RogerHao/cosmo-pager-radio-demo/pcb/cosmoradio-v4-carrier/output/renders/bottom.png

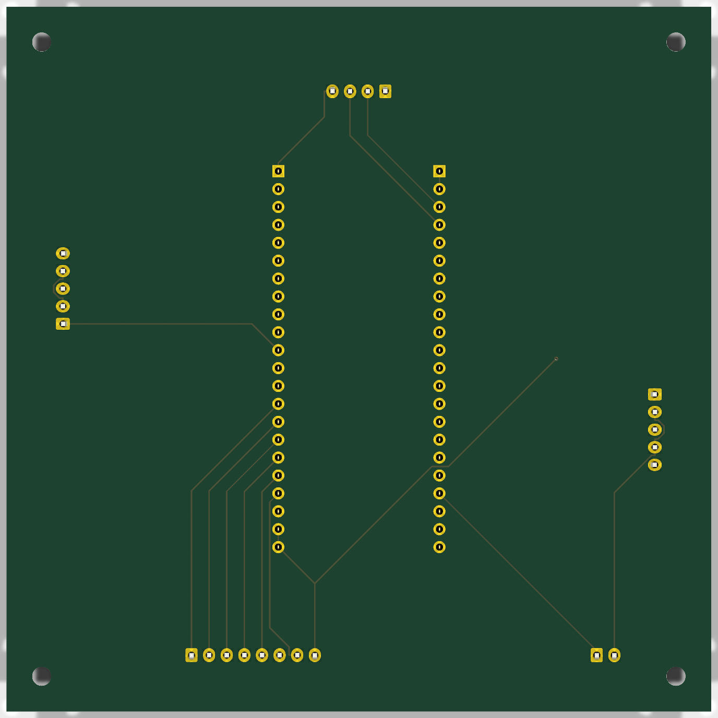
pcb/cosmoradio-v4-carrier/output/renders/bottom.png
