RogerHao/cosmo-pager-radio-demo/pcb/cosmoradio-v4-carrier/output/renders/iso.png

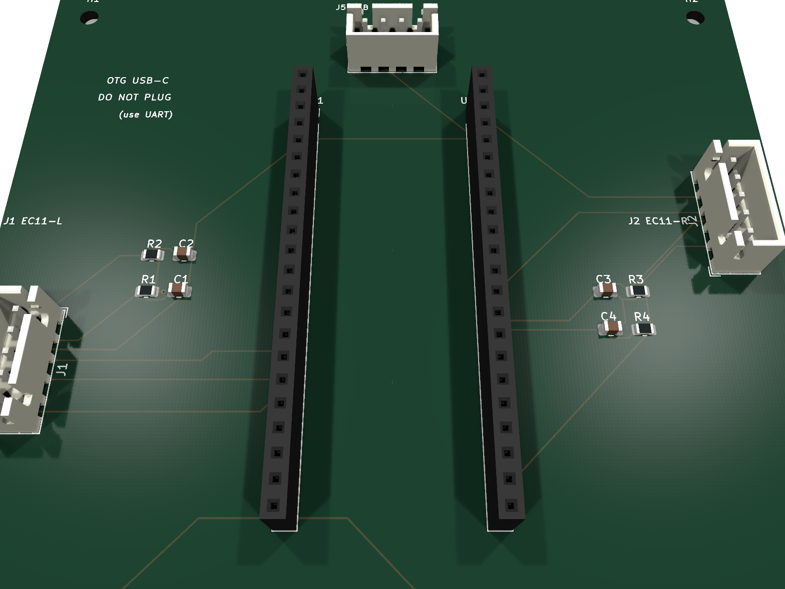
pcb/cosmoradio-v4-carrier/output/renders/iso.png
