RogerHao/cosmo-pager-radio-demo/pcb/cosmoradio-v4-carrier/output/renders/top.png

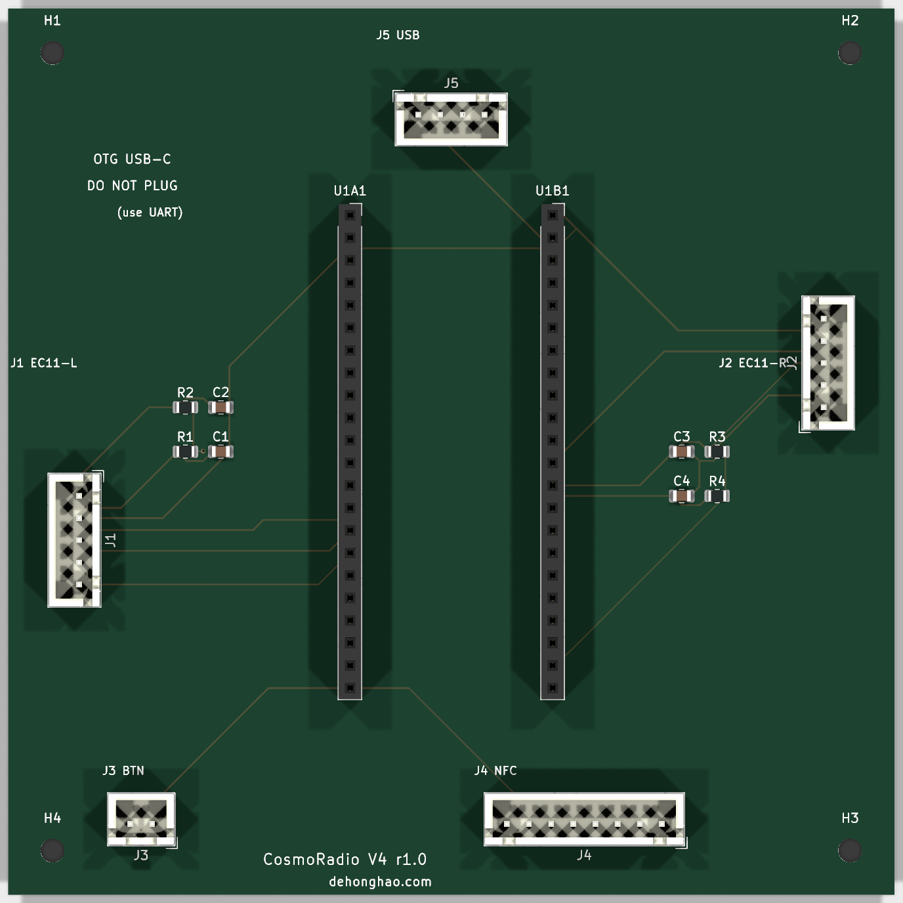
pcb/cosmoradio-v4-carrier/output/renders/top.png
