RogerHao/cosmo-pager-radio-demo/firmware/main/esp_hid_gap.c

/*
 * SPDX-FileCopyrightText: 2021-2024 Espressif Systems (Shanghai) CO LTD
 *
 * SPDX-License-Identifier: Unlicense OR CC0-1.0
 */


#include <string.h>
#include <stdbool.h>
#include <inttypes.h>

#include "freertos/FreeRTOS.h"
#include "freertos/task.h"
#include "freertos/semphr.h"

#include "esp_hid_gap.h"

#if CONFIG_BT_NIMBLE_ENABLED
#include "host/ble_hs.h"
#include "nimble/nimble_port.h"
#include "host/ble_gap.h"
#include "host/ble_hs_adv.h"
#include "nimble/ble.h"
#include "host/ble_sm.h"
#include "store/config/ble_store_config.h"
#else
#include "esp_bt_device.h"
#endif

static const char *TAG = "ESP_HID_GAP";

// uncomment to print all devices that were seen during a scan
#define GAP_DBG_PRINTF(...) //printf(__VA_ARGS__)
//static const char * gap_bt_prop_type_names[5] = {"","BDNAME","COD","RSSI","EIR"};

#if !CONFIG_BT_NIMBLE_ENABLED
static esp_hid_scan_result_t *bt_scan_results = NULL;
static size_t num_bt_scan_results = 0;

static esp_hid_scan_result_t *ble_scan_results = NULL;
static size_t num_ble_scan_results = 0;
#endif

static SemaphoreHandle_t bt_hidh_cb_semaphore = NULL;
#define WAIT_BT_CB() xSemaphoreTake(bt_hidh_cb_semaphore, portMAX_DELAY)
#define SEND_BT_CB() xSemaphoreGive(bt_hidh_cb_semaphore)

static SemaphoreHandle_t ble_hidh_cb_semaphore = NULL;
#define WAIT_BLE_CB() xSemaphoreTake(ble_hidh_cb_semaphore, portMAX_DELAY)
#define SEND_BLE_CB() xSemaphoreGive(ble_hidh_cb_semaphore)

#define SIZEOF_ARRAY(a) (sizeof(a)/sizeof(*a))

#if !CONFIG_BT_NIMBLE_ENABLED
static const char *ble_gap_evt_names[] = { "ADV_DATA_SET_COMPLETE", "SCAN_RSP_DATA_SET_COMPLETE", "SCAN_PARAM_SET_COMPLETE", "SCAN_RESULT", "ADV_DATA_RAW_SET_COMPLETE", "SCAN_RSP_DATA_RAW_SET_COMPLETE", "ADV_START_COMPLETE", "SCAN_START_COMPLETE", "AUTH_CMPL", "KEY", "SEC_REQ", "PASSKEY_NOTIF", "PASSKEY_REQ", "OOB_REQ", "LOCAL_IR", "LOCAL_ER", "NC_REQ", "ADV_STOP_COMPLETE", "SCAN_STOP_COMPLETE", "SET_STATIC_RAND_ADDR", "UPDATE_CONN_PARAMS", "SET_PKT_LENGTH_COMPLETE", "SET_LOCAL_PRIVACY_COMPLETE", "REMOVE_BOND_DEV_COMPLETE", "CLEAR_BOND_DEV_COMPLETE", "GET_BOND_DEV_COMPLETE", "READ_RSSI_COMPLETE", "UPDATE_WHITELIST_COMPLETE"};
static const char *bt_gap_evt_names[] = { "DISC_RES", "DISC_STATE_CHANGED", "RMT_SRVCS", "RMT_SRVC_REC", "AUTH_CMPL", "PIN_REQ", "CFM_REQ", "KEY_NOTIF", "KEY_REQ", "READ_RSSI_DELTA"};
static const char *ble_addr_type_names[] = {"PUBLIC", "RANDOM", "RPA_PUBLIC", "RPA_RANDOM"};

const char *ble_addr_type_str(esp_ble_addr_type_t ble_addr_type)
{
    if (ble_addr_type > BLE_ADDR_TYPE_RPA_RANDOM) {
        return "UNKNOWN";
    }
    return ble_addr_type_names[ble_addr_type];
}

const char *ble_gap_evt_str(uint8_t event)
{
    if (event >= SIZEOF_ARRAY(ble_gap_evt_names)) {
        return "UNKNOWN";
    }
    return ble_gap_evt_names[event];
}

const char *bt_gap_evt_str(uint8_t event)
{
    if (event >= SIZEOF_ARRAY(bt_gap_evt_names)) {
        return "UNKNOWN";
    }
    return bt_gap_evt_names[event];
}
#endif

#if CONFIG_BT_BLE_ENABLED
const char *esp_ble_key_type_str(esp_ble_key_type_t key_type)
{
    const char *key_str = NULL;
    switch (key_type) {
    case ESP_LE_KEY_NONE:
        key_str = "ESP_LE_KEY_NONE";
        break;
    case ESP_LE_KEY_PENC:
        key_str = "ESP_LE_KEY_PENC";
        break;
    case ESP_LE_KEY_PID:
        key_str = "ESP_LE_KEY_PID";
        break;
    case ESP_LE_KEY_PCSRK:
        key_str = "ESP_LE_KEY_PCSRK";
        break;
    case ESP_LE_KEY_PLK:
        key_str = "ESP_LE_KEY_PLK";
        break;
    case ESP_LE_KEY_LLK:
        key_str = "ESP_LE_KEY_LLK";
        break;
    case ESP_LE_KEY_LENC:
        key_str = "ESP_LE_KEY_LENC";
        break;
    case ESP_LE_KEY_LID:
        key_str = "ESP_LE_KEY_LID";
        break;
    case ESP_LE_KEY_LCSRK:
        key_str = "ESP_LE_KEY_LCSRK";
        break;
    default:
        key_str = "INVALID BLE KEY TYPE";
        break;

    }
    return key_str;
}
#endif /* CONFIG_BT_BLE_ENABLED */

#if !CONFIG_BT_NIMBLE_ENABLED
void esp_hid_scan_results_free(esp_hid_scan_result_t *results)
{
    esp_hid_scan_result_t *r = NULL;
    while (results) {
        r = results;
        results = results->next;
        if (r->name != NULL) {
            free((char *)r->name);
        }
        free(r);
    }
}
#endif

#if (CONFIG_BT_HID_DEVICE_ENABLED || CONFIG_BT_BLE_ENABLED)
static esp_hid_scan_result_t *find_scan_result(esp_bd_addr_t bda, esp_hid_scan_result_t *results)
{
    esp_hid_scan_result_t *r = results;
    while (r) {
        if (memcmp(bda, r->bda, sizeof(esp_bd_addr_t)) == 0) {
            return r;
        }
        r = r->next;
    }
    return NULL;
}
#endif /* (CONFIG_BT_HID_DEVICE_ENABLED || CONFIG_BT_BLE_ENABLED) */

#if CONFIG_BT_HID_DEVICE_ENABLED
static void add_bt_scan_result(esp_bd_addr_t bda, esp_bt_cod_t *cod, esp_bt_uuid_t *uuid, uint8_t *name, uint8_t name_len, int rssi)
{
    esp_hid_scan_result_t *r = find_scan_result(bda, bt_scan_results);
    if (r) {
        //Some info may come later
        if (r->name == NULL && name && name_len) {
            char *name_s = (char *)malloc(name_len + 1);
            if (name_s == NULL) {
                ESP_LOGE(TAG, "Malloc result name failed!");
                return;
            }
            memcpy(name_s, name, name_len);
            name_s[name_len] = 0;
            r->name = (const char *)name_s;
        }
        if (r->bt.uuid.len == 0 && uuid->len) {
            memcpy(&r->bt.uuid, uuid, sizeof(esp_bt_uuid_t));
        }
        if (rssi != 0) {
            r->rssi = rssi;
        }
        return;
    }

    r = (esp_hid_scan_result_t *)malloc(sizeof(esp_hid_scan_result_t));
    if (r == NULL) {
        ESP_LOGE(TAG, "Malloc bt_hidh_scan_result_t failed!");
        return;
    }
    r->transport = ESP_HID_TRANSPORT_BT;
    memcpy(r->bda, bda, sizeof(esp_bd_addr_t));
    memcpy(&r->bt.cod, cod, sizeof(esp_bt_cod_t));
    memcpy(&r->bt.uuid, uuid, sizeof(esp_bt_uuid_t));
    r->usage = esp_hid_usage_from_cod((uint32_t)cod);
    r->rssi = rssi;
    r->name = NULL;
    if (name_len && name) {
        char *name_s = (char *)malloc(name_len + 1);
        if (name_s == NULL) {
            free(r);
            ESP_LOGE(TAG, "Malloc result name failed!");
            return;
        }
        memcpy(name_s, name, name_len);
        name_s[name_len] = 0;
        r->name = (const char *)name_s;
    }
    r->next = bt_scan_results;
    bt_scan_results = r;
    num_bt_scan_results++;
}
#endif

#if CONFIG_BT_BLE_ENABLED
static void add_ble_scan_result(esp_bd_addr_t bda, esp_ble_addr_type_t addr_type, uint16_t appearance, uint8_t *name, uint8_t name_len, int rssi)
{
    if (find_scan_result(bda, ble_scan_results)) {
        ESP_LOGW(TAG, "Result already exists!");
        return;
    }
    esp_hid_scan_result_t *r = (esp_hid_scan_result_t *)malloc(sizeof(esp_hid_scan_result_t));
    if (r == NULL) {
        ESP_LOGE(TAG, "Malloc ble_hidh_scan_result_t failed!");
        return;
    }
    r->transport = ESP_HID_TRANSPORT_BLE;
    memcpy(r->bda, bda, sizeof(esp_bd_addr_t));
    r->ble.appearance = appearance;
    r->ble.addr_type = addr_type;
    r->usage = esp_hid_usage_from_appearance(appearance);
    r->rssi = rssi;
    r->name = NULL;
    if (name_len && name) {
        char *name_s = (char *)malloc(name_len + 1);
        if (name_s == NULL) {
            free(r);
            ESP_LOGE(TAG, "Malloc result name failed!");
            return;
        }
        memcpy(name_s, name, name_len);
        name_s[name_len] = 0;
        r->name = (const char *)name_s;
    }
    r->next = ble_scan_results;
    ble_scan_results = r;
    num_ble_scan_results++;
}
#endif /* CONFIG_BT_BLE_ENABLED */

#if !CONFIG_BT_NIMBLE_ENABLED
void print_uuid(esp_bt_uuid_t *uuid)
{
    if (uuid->len == ESP_UUID_LEN_16) {
        GAP_DBG_PRINTF("UUID16: 0x%04x", uuid->uuid.uuid16);
    } else if (uuid->len == ESP_UUID_LEN_32) {
        GAP_DBG_PRINTF("UUID32: 0x%08x", uuid->uuid.uuid32);
    } else if (uuid->len == ESP_UUID_LEN_128) {
        GAP_DBG_PRINTF("UUID128: %02x,%02x,%02x,%02x,%02x,%02x,%02x,%02x,%02x,%02x,%02x,%02x,%02x,%02x,%02x,%02x", uuid->uuid.uuid128[0],
                       uuid->uuid.uuid128[1], uuid->uuid.uuid128[2], uuid->uuid.uuid128[3],
                       uuid->uuid.uuid128[4], uuid->uuid.uuid128[5], uuid->uuid.uuid128[6],
                       uuid->uuid.uuid128[7], uuid->uuid.uuid128[8], uuid->uuid.uuid128[9],
                       uuid->uuid.uuid128[10], uuid->uuid.uuid128[11], uuid->uuid.uuid128[12],
                       uuid->uuid.uuid128[13], uuid->uuid.uuid128[14], uuid->uuid.uuid128[15]);
    }
}
#endif

#if CONFIG_BT_HID_DEVICE_ENABLED
static void handle_bt_device_result(struct disc_res_param *disc_res)
{
    GAP_DBG_PRINTF("BT : " ESP_BD_ADDR_STR, ESP_BD_ADDR_HEX(disc_res->bda));
    uint32_t codv = 0;
    esp_bt_cod_t *cod = (esp_bt_cod_t *)&codv;
    int8_t rssi = 0;
    uint8_t *name = NULL;
    uint8_t name_len = 0;
    esp_bt_uuid_t uuid;

    uuid.len = ESP_UUID_LEN_16;
    uuid.uuid.uuid16 = 0;

    for (int i = 0; i < disc_res->num_prop; i++) {
        esp_bt_gap_dev_prop_t *prop = &disc_res->prop[i];
        if (prop->type != ESP_BT_GAP_DEV_PROP_EIR) {
            GAP_DBG_PRINTF(", %s: ", gap_bt_prop_type_names[prop->type]);
        }
        if (prop->type == ESP_BT_GAP_DEV_PROP_BDNAME) {
            name = (uint8_t *)prop->val;
            name_len = strlen((const char *)name);
            GAP_DBG_PRINTF("%s", (const char *)name);
        } else if (prop->type == ESP_BT_GAP_DEV_PROP_RSSI) {
            rssi = *((int8_t *)prop->val);
            GAP_DBG_PRINTF("%d", rssi);
        } else if (prop->type == ESP_BT_GAP_DEV_PROP_COD) {
            memcpy(&codv, prop->val, sizeof(uint32_t));
            GAP_DBG_PRINTF("major: %s, minor: %d, service: 0x%03x", esp_hid_cod_major_str(cod->major), cod->minor, cod->service);
        } else if (prop->type == ESP_BT_GAP_DEV_PROP_EIR) {
            uint8_t len = 0;
            uint8_t *data = 0;

            data = esp_bt_gap_resolve_eir_data((uint8_t *)prop->val, ESP_BT_EIR_TYPE_CMPL_16BITS_UUID, &len);
            if (data == NULL) {
                data = esp_bt_gap_resolve_eir_data((uint8_t *)prop->val, ESP_BT_EIR_TYPE_INCMPL_16BITS_UUID, &len);
            }
            if (data && len == ESP_UUID_LEN_16) {
                uuid.len = ESP_UUID_LEN_16;
                uuid.uuid.uuid16 = data[0] + (data[1] << 8);
                GAP_DBG_PRINTF(", "); print_uuid(&uuid);
                continue;
            }

            data = esp_bt_gap_resolve_eir_data((uint8_t *)prop->val, ESP_BT_EIR_TYPE_CMPL_32BITS_UUID, &len);
            if (data == NULL) {
                data = esp_bt_gap_resolve_eir_data((uint8_t *)prop->val, ESP_BT_EIR_TYPE_INCMPL_32BITS_UUID, &len);
            }
            if (data && len == ESP_UUID_LEN_32) {
                uuid.len = len;
                memcpy(&uuid.uuid.uuid32, data, sizeof(uint32_t));
                GAP_DBG_PRINTF(", "); print_uuid(&uuid);
                continue;
            }

            data = esp_bt_gap_resolve_eir_data((uint8_t *)prop->val, ESP_BT_EIR_TYPE_CMPL_128BITS_UUID, &len);
            if (data == NULL) {
                data = esp_bt_gap_resolve_eir_data((uint8_t *)prop->val, ESP_BT_EIR_TYPE_INCMPL_128BITS_UUID, &len);
            }
            if (data && len == ESP_UUID_LEN_128) {
                uuid.len = len;
                memcpy(uuid.uuid.uuid128, (uint8_t *)data, len);
                GAP_DBG_PRINTF(", "); print_uuid(&uuid);
                continue;
            }

            //try to find a name
            if (name == NULL) {
                data = esp_bt_gap_resolve_eir_data((uint8_t *)prop->val, ESP_BT_EIR_TYPE_CMPL_LOCAL_NAME, &len);
                if (data == NULL) {
                    data = esp_bt_gap_resolve_eir_data((uint8_t *)prop->val, ESP_BT_EIR_TYPE_SHORT_LOCAL_NAME, &len);
                }
                if (data && len) {
                    name = data;
                    name_len = len;
                    GAP_DBG_PRINTF(", NAME: ");
                    for (int x = 0; x < len; x++) {
                        GAP_DBG_PRINTF("%c", (char)data[x]);
                    }
                }
            }
        }
    }
    GAP_DBG_PRINTF("\n");

    if (cod->major == ESP_BT_COD_MAJOR_DEV_PERIPHERAL || (find_scan_result(disc_res->bda, bt_scan_results) != NULL)) {
        add_bt_scan_result(disc_res->bda, cod, &uuid, name, name_len, rssi);
    }
}
#endif

#if CONFIG_BT_BLE_ENABLED
static void handle_ble_device_result(struct ble_scan_result_evt_param *scan_rst)
{

    uint16_t uuid = 0;
    uint16_t appearance = 0;
    char name[64] = {0};

    uint8_t uuid_len = 0;
    uint8_t *uuid_d = esp_ble_resolve_adv_data_by_type(scan_rst->ble_adv,
                      scan_rst->adv_data_len + scan_rst->scan_rsp_len,
                      ESP_BLE_AD_TYPE_16SRV_CMPL,
                      &uuid_len);
    if (uuid_d != NULL && uuid_len) {
        uuid = uuid_d[0] + (uuid_d[1] << 8);
    }

    uint8_t appearance_len = 0;
    uint8_t *appearance_d = esp_ble_resolve_adv_data_by_type(scan_rst->ble_adv,
                                                    scan_rst->adv_data_len + scan_rst->scan_rsp_len,
                                                    ESP_BLE_AD_TYPE_APPEARANCE,
                                                    &appearance_len);
    if (appearance_d != NULL && appearance_len) {
        appearance = appearance_d[0] + (appearance_d[1] << 8);
    }

    uint8_t adv_name_len = 0;
    uint8_t *adv_name = esp_ble_resolve_adv_data_by_type(scan_rst->ble_adv,
                                                 scan_rst->adv_data_len + scan_rst->scan_rsp_len,
                                                 ESP_BLE_AD_TYPE_NAME_CMPL,
                                                 &adv_name_len);

    if (adv_name == NULL) {
        adv_name = esp_ble_resolve_adv_data_by_type(scan_rst->ble_adv,
                                            scan_rst->adv_data_len + scan_rst->scan_rsp_len,
                                            ESP_BLE_AD_TYPE_NAME_SHORT,
                                            &adv_name_len);
    }

    if (adv_name != NULL && adv_name_len) {
        memcpy(name, adv_name, adv_name_len);
        name[adv_name_len] = 0;
    }

    GAP_DBG_PRINTF("BLE: " ESP_BD_ADDR_STR ", ", ESP_BD_ADDR_HEX(scan_rst->bda));
    GAP_DBG_PRINTF("RSSI: %d, ", scan_rst->rssi);
    GAP_DBG_PRINTF("UUID: 0x%04x, ", uuid);
    GAP_DBG_PRINTF("APPEARANCE: 0x%04x, ", appearance);
    GAP_DBG_PRINTF("ADDR_TYPE: '%s'", ble_addr_type_str(scan_rst->ble_addr_type));
    if (adv_name_len) {
        GAP_DBG_PRINTF(", NAME: '%s'", name);
    }
    GAP_DBG_PRINTF("\n");

    if (uuid == ESP_GATT_UUID_HID_SVC) {
        add_ble_scan_result(scan_rst->bda, scan_rst->ble_addr_type, appearance, adv_name, adv_name_len, scan_rst->rssi);
    }
}
#endif /* CONFIG_BT_BLE_ENABLED */

#if CONFIG_BT_HID_DEVICE_ENABLED
/*
 * BT GAP
 * */

static void bt_gap_event_handler(esp_bt_gap_cb_event_t event, esp_bt_gap_cb_param_t *param)
{
    switch (event) {
    case ESP_BT_GAP_DISC_STATE_CHANGED_EVT: {
        ESP_LOGV(TAG, "BT GAP DISC_STATE %s", (param->disc_st_chg.state == ESP_BT_GAP_DISCOVERY_STARTED) ? "START" : "STOP");
        if (param->disc_st_chg.state == ESP_BT_GAP_DISCOVERY_STOPPED) {
            SEND_BT_CB();
        }
        break;
    }
    case ESP_BT_GAP_DISC_RES_EVT: {
        handle_bt_device_result(&param->disc_res);
        break;
    }
    case ESP_BT_GAP_PIN_REQ_EVT: {
        ESP_LOGI(TAG, "BT GAP PIN_REQ_EVT min_16_digit:%d", param->pin_req.min_16_digit);
        if (param->pin_req.min_16_digit) {
            ESP_LOGI(TAG, "Input pin code: 0000 0000 0000 0000");
            esp_bt_pin_code_t pin_code = {0};
            esp_bt_gap_pin_reply(param->pin_req.bda, true, 16, pin_code);
        } else {
            ESP_LOGI(TAG, "Input pin code: 1234");
            esp_bt_pin_code_t pin_code;
            pin_code[0] = '1';
            pin_code[1] = '2';
            pin_code[2] = '3';
            pin_code[3] = '4';
            esp_bt_gap_pin_reply(param->pin_req.bda, true, 4, pin_code);
        }
        break;
    }

#if (CONFIG_EXAMPLE_SSP_ENABLED == true)
    case ESP_BT_GAP_CFM_REQ_EVT:
        ESP_LOGI(TAG, "BT GAP CFM_REQ_EVT Please compare the numeric value: %06" PRIu32,
                 param->cfm_req.num_val);
        esp_bt_gap_ssp_confirm_reply(param->cfm_req.bda, true);
        break;
    case ESP_BT_GAP_KEY_NOTIF_EVT:
        ESP_LOGI(TAG, "BT GAP KEY_NOTIF_EVT passkey:%06" PRIu32, param->key_notif.passkey);
        break;
    case ESP_BT_GAP_KEY_REQ_EVT:
        ESP_LOGI(TAG, "BT GAP KEY_REQ_EVT Please enter passkey!");
        break;
#endif
    case ESP_BT_GAP_MODE_CHG_EVT:
        ESP_LOGI(TAG, "BT GAP MODE_CHG_EVT mode:%d", param->mode_chg.mode);
        break;
    default:
        ESP_LOGV(TAG, "BT GAP EVENT %s", bt_gap_evt_str(event));
        break;
    }
}

static esp_err_t init_bt_gap(void)
{
    esp_err_t ret;
#if (CONFIG_EXAMPLE_SSP_ENABLED)
    /* Set default parameters for Secure Simple Pairing */
    esp_bt_sp_param_t param_type = ESP_BT_SP_IOCAP_MODE;
    esp_bt_io_cap_t iocap = ESP_BT_IO_CAP_NONE;
    esp_bt_gap_set_security_param(param_type, &iocap, sizeof(uint8_t));
#endif
    /*
     * Set default parameters for Legacy Pairing
     * Use fixed pin code
     */
    esp_bt_pin_type_t pin_type = ESP_BT_PIN_TYPE_FIXED;
    esp_bt_pin_code_t pin_code;
    pin_code[0] = '1';
    pin_code[1] = '2';
    pin_code[2] = '3';
    pin_code[3] = '4';
    esp_bt_gap_set_pin(pin_type, 4, pin_code);

    if ((ret = esp_bt_gap_register_callback(bt_gap_event_handler)) != ESP_OK) {
        ESP_LOGE(TAG, "esp_bt_gap_register_callback failed: %d", ret);
        return ret;
    }

    // Allow BT devices to connect back to us
    if ((ret = esp_bt_gap_set_scan_mode(ESP_BT_CONNECTABLE, ESP_BT_NON_DISCOVERABLE)) != ESP_OK) {
        ESP_LOGE(TAG, "esp_bt_gap_set_scan_mode failed: %d", ret);
        return ret;
    }
    return ret;
}

static esp_err_t start_bt_scan(uint32_t seconds)
{
    esp_err_t ret = ESP_OK;
    if ((ret = esp_bt_gap_start_discovery(ESP_BT_INQ_MODE_GENERAL_INQUIRY, (int)(seconds / 1.28), 0)) != ESP_OK) {
        ESP_LOGE(TAG, "esp_bt_gap_start_discovery failed: %d", ret);
        return ret;
    }
    return ret;
}
#endif

#if CONFIG_BT_BLE_ENABLED
/*
 * BLE GAP
 * */
extern void ble_hid_task_start_up(void);
static void ble_gap_event_handler(esp_gap_ble_cb_event_t event, esp_ble_gap_cb_param_t *param)
{
    switch (event) {
    /*
     * SCAN
     * */
    case ESP_GAP_BLE_SCAN_PARAM_SET_COMPLETE_EVT: {
        ESP_LOGV(TAG, "BLE GAP EVENT SCAN_PARAM_SET_COMPLETE");
        SEND_BLE_CB();
        break;
    }
    case ESP_GAP_BLE_SCAN_RESULT_EVT: {
        esp_ble_gap_cb_param_t *scan_result = (esp_ble_gap_cb_param_t *)param;
        switch (scan_result->scan_rst.search_evt) {
        case ESP_GAP_SEARCH_INQ_RES_EVT: {
            handle_ble_device_result(&scan_result->scan_rst);
            break;
        }
        case ESP_GAP_SEARCH_INQ_CMPL_EVT:
            ESP_LOGV(TAG, "BLE GAP EVENT SCAN DONE: %d", scan_result->scan_rst.num_resps);
            SEND_BLE_CB();
            break;
        default:
            break;
        }
        break;
    }
    case ESP_GAP_BLE_SCAN_STOP_COMPLETE_EVT: {
        ESP_LOGV(TAG, "BLE GAP EVENT SCAN CANCELED");
        break;
    }

    /*
     * ADVERTISEMENT
     * */
    case ESP_GAP_BLE_ADV_DATA_SET_COMPLETE_EVT:
        ESP_LOGV(TAG, "BLE GAP ADV_DATA_SET_COMPLETE");
        break;

    case ESP_GAP_BLE_ADV_START_COMPLETE_EVT:
        ESP_LOGV(TAG, "BLE GAP ADV_START_COMPLETE");
        break;

    /*
     * AUTHENTICATION
     * */
    case ESP_GAP_BLE_AUTH_CMPL_EVT:
        if (!param->ble_security.auth_cmpl.success) {
            // if AUTH ERROR,hid maybe don't work.
            ESP_LOGE(TAG, "BLE GAP AUTH ERROR: 0x%x", param->ble_security.auth_cmpl.fail_reason);
        } else {
            ESP_LOGI(TAG, "BLE GAP AUTH SUCCESS");
        }
        ble_hid_task_start_up();
        break;

    case ESP_GAP_BLE_KEY_EVT: //shows the ble key info share with peer device to the user.
        ESP_LOGI(TAG, "BLE GAP KEY type = %s", esp_ble_key_type_str(param->ble_security.ble_key.key_type));
        break;

    case ESP_GAP_BLE_PASSKEY_NOTIF_EVT: // ESP_IO_CAP_OUT
        // The app will receive this evt when the IO has Output capability and the peer device IO has Input capability.
        // Show the passkey number to the user to input it in the peer device.
        ESP_LOGI(TAG, "BLE GAP PASSKEY_NOTIF passkey:%"PRIu32, param->ble_security.key_notif.passkey);
        break;

    case ESP_GAP_BLE_NC_REQ_EVT: // ESP_IO_CAP_IO
        // The app will receive this event when the IO has DisplayYesNO capability and the peer device IO also has DisplayYesNo capability.
        // show the passkey number to the user to confirm it with the number displayed by peer device.
        ESP_LOGI(TAG, "BLE GAP NC_REQ passkey:%"PRIu32, param->ble_security.key_notif.passkey);
        esp_ble_confirm_reply(param->ble_security.key_notif.bd_addr, true);
        break;

    case ESP_GAP_BLE_PASSKEY_REQ_EVT: // ESP_IO_CAP_IN
        // The app will receive this evt when the IO has Input capability and the peer device IO has Output capability.
        // See the passkey number on the peer device and send it back.
        ESP_LOGI(TAG, "BLE GAP PASSKEY_REQ");
        //esp_ble_passkey_reply(param->ble_security.ble_req.bd_addr, true, 1234);
        break;

    case ESP_GAP_BLE_SEC_REQ_EVT:
        ESP_LOGI(TAG, "BLE GAP SEC_REQ");
        // Send the positive(true) security response to the peer device to accept the security request.
        // If not accept the security request, should send the security response with negative(false) accept value.
        esp_ble_gap_security_rsp(param->ble_security.ble_req.bd_addr, true);
        break;

    default:
        ESP_LOGV(TAG, "BLE GAP EVENT %s", ble_gap_evt_str(event));
        break;
    }
}

static esp_err_t init_ble_gap(void)
{
    esp_err_t ret;

    if ((ret = esp_ble_gap_register_callback(ble_gap_event_handler)) != ESP_OK) {
        ESP_LOGE(TAG, "esp_ble_gap_register_callback failed: %d", ret);
        return ret;
    }
    return ret;
}

static esp_ble_scan_params_t hid_scan_params = {
    .scan_type              = BLE_SCAN_TYPE_ACTIVE,
    .own_addr_type          = BLE_ADDR_TYPE_PUBLIC,
    .scan_filter_policy     = BLE_SCAN_FILTER_ALLOW_ALL,
    .scan_interval          = 0x50,
    .scan_window            = 0x30,
    .scan_duplicate         = BLE_SCAN_DUPLICATE_ENABLE,
};

static esp_err_t start_ble_scan(uint32_t seconds)
{
    esp_err_t ret = ESP_OK;
    if ((ret = esp_ble_gap_set_scan_params(&hid_scan_params)) != ESP_OK) {
        ESP_LOGE(TAG, "esp_ble_gap_set_scan_params failed: %d", ret);
        return ret;
    }
    WAIT_BLE_CB();

    if ((ret = esp_ble_gap_start_scanning(seconds)) != ESP_OK) {
        ESP_LOGE(TAG, "esp_ble_gap_start_scanning failed: %d", ret);
        return ret;
    }
    return ret;
}

#if !CONFIG_BT_NIMBLE_ENABLED
esp_err_t esp_hid_ble_gap_adv_init(uint16_t appearance, const char *device_name)
{

    esp_err_t ret;

    const uint8_t hidd_service_uuid128[] = {
        0xfb, 0x34, 0x9b, 0x5f, 0x80, 0x00, 0x00, 0x80, 0x00, 0x10, 0x00, 0x00, 0x12, 0x18, 0x00, 0x00,
    };

    esp_ble_adv_data_t ble_adv_data = {
        .set_scan_rsp = false,
        .include_name = true,
        .include_txpower = true,
        .min_interval = 0x0006, //slave connection min interval, Time = min_interval * 1.25 msec
        .max_interval = 0x0010, //slave connection max interval, Time = max_interval * 1.25 msec
        .appearance = appearance,
        .manufacturer_len = 0,
        .p_manufacturer_data =  NULL,
        .service_data_len = 0,
        .p_service_data = NULL,
        .service_uuid_len = sizeof(hidd_service_uuid128),
        .p_service_uuid = (uint8_t *)hidd_service_uuid128,
        .flag = 0x6,
    };

    esp_ble_auth_req_t auth_req = ESP_LE_AUTH_REQ_SC_MITM_BOND;
    //esp_ble_io_cap_t iocap = ESP_IO_CAP_OUT;//you have to enter the key on the host
    //esp_ble_io_cap_t iocap = ESP_IO_CAP_IN;//you have to enter the key on the device
    esp_ble_io_cap_t iocap = ESP_IO_CAP_IO;//you have to agree that key matches on both
    //esp_ble_io_cap_t iocap = ESP_IO_CAP_NONE;//device is not capable of input or output, insecure
    uint8_t init_key = ESP_BLE_ENC_KEY_MASK | ESP_BLE_ID_KEY_MASK;
    uint8_t rsp_key = ESP_BLE_ENC_KEY_MASK | ESP_BLE_ID_KEY_MASK;
    uint8_t key_size = 16; //the key size should be 7~16 bytes
    uint32_t passkey = 1234;//ESP_IO_CAP_OUT

    if ((ret = esp_ble_gap_set_security_param(ESP_BLE_SM_AUTHEN_REQ_MODE, &auth_req, 1)) != ESP_OK) {
        ESP_LOGE(TAG, "GAP set_security_param AUTHEN_REQ_MODE failed: %d", ret);
        return ret;
    }

    if ((ret = esp_ble_gap_set_security_param(ESP_BLE_SM_IOCAP_MODE, &iocap, 1)) != ESP_OK) {
        ESP_LOGE(TAG, "GAP set_security_param IOCAP_MODE failed: %d", ret);
        return ret;
    }

    if ((ret = esp_ble_gap_set_security_param(ESP_BLE_SM_SET_INIT_KEY, &init_key, 1)) != ESP_OK) {
        ESP_LOGE(TAG, "GAP set_security_param SET_INIT_KEY failed: %d", ret);
        return ret;
    }

    if ((ret = esp_ble_gap_set_security_param(ESP_BLE_SM_SET_RSP_KEY, &rsp_key, 1)) != ESP_OK) {
        ESP_LOGE(TAG, "GAP set_security_param SET_RSP_KEY failed: %d", ret);
        return ret;
    }

    if ((ret = esp_ble_gap_set_security_param(ESP_BLE_SM_MAX_KEY_SIZE, &key_size, 1)) != ESP_OK) {
        ESP_LOGE(TAG, "GAP set_security_param MAX_KEY_SIZE failed: %d", ret);
        return ret;
    }

    if ((ret = esp_ble_gap_set_security_param(ESP_BLE_SM_SET_STATIC_PASSKEY, &passkey, sizeof(uint32_t))) != ESP_OK) {
        ESP_LOGE(TAG, "GAP set_security_param SET_STATIC_PASSKEY failed: %d", ret);
        return ret;
    }

    if ((ret = esp_ble_gap_set_device_name(device_name)) != ESP_OK) {
        ESP_LOGE(TAG, "GAP set_device_name failed: %d", ret);
        return ret;
    }

    if ((ret = esp_ble_gap_config_adv_data(&ble_adv_data)) != ESP_OK) {
        ESP_LOGE(TAG, "GAP config_adv_data failed: %d", ret);
        return ret;
    }

    return ret;
}
#endif
esp_err_t esp_hid_ble_gap_adv_start(void)
{
    static esp_ble_adv_params_t hidd_adv_params = {
        .adv_int_min        = 0x20,
        .adv_int_max        = 0x30,
        .adv_type           = ADV_TYPE_IND,
        .own_addr_type      = BLE_ADDR_TYPE_PUBLIC,
        .channel_map        = ADV_CHNL_ALL,
        .adv_filter_policy  = ADV_FILTER_ALLOW_SCAN_ANY_CON_ANY,
    };
    return esp_ble_gap_start_advertising(&hidd_adv_params);
}
#endif /* CONFIG_BT_BLE_ENABLED */

#if CONFIG_BT_NIMBLE_ENABLED
#define GATT_SVR_SVC_HID_UUID 0x1812

extern void ble_hid_task_start_up(void);
static struct ble_hs_adv_fields fields;

esp_err_t esp_hid_ble_gap_adv_init(uint16_t appearance, const char *device_name)
{
    ble_uuid16_t *uuid16, *uuid16_1;
    /**
     *  Set the advertisement data included in our advertisements:
     *     o Flags (indicates advertisement type and other general info).
     *     o Advertising tx power.
     *     o Device name.
     *     o 16-bit service UUIDs (HID).
     */

    memset(&fields, 0, sizeof fields);

    /* Advertise two flags:
     *     o Discoverability in forthcoming advertisement (general)
     *     o BLE-only (BR/EDR unsupported).
     */
    fields.flags = BLE_HS_ADV_F_DISC_GEN |
                   BLE_HS_ADV_F_BREDR_UNSUP;

    fields.appearance = ESP_HID_APPEARANCE_GENERIC;
    fields.appearance_is_present = 1;

    /* Indicate that the TX power level field should be included; have the
     * stack fill this value automatically.  This is done by assigning the
     * special value BLE_HS_ADV_TX_PWR_LVL_AUTO.
     */
    fields.tx_pwr_lvl_is_present = 1;
    fields.tx_pwr_lvl = BLE_HS_ADV_TX_PWR_LVL_AUTO;

    fields.name = (uint8_t *)device_name;
    fields.name_len = strlen(device_name);
    fields.name_is_complete = 1;

    uuid16 = (ble_uuid16_t *)malloc(sizeof(ble_uuid16_t));
    uuid16_1 = (ble_uuid16_t[]) {
        BLE_UUID16_INIT(GATT_SVR_SVC_HID_UUID)
    };
    memcpy(uuid16, uuid16_1, sizeof(ble_uuid16_t));
    fields.uuids16 = uuid16;
    fields.num_uuids16 = 1;
    fields.uuids16_is_complete = 1;

    /* Initialize the security configuration */
    /* Use "Just Works" pairing - no PIN required */
    ble_hs_cfg.sm_io_cap = BLE_SM_IO_CAP_NO_IO;
    ble_hs_cfg.sm_bonding = 1;
    ble_hs_cfg.sm_mitm = 0;  // Disable MITM for Just Works
    ble_hs_cfg.sm_sc = 1;
    ble_hs_cfg.sm_our_key_dist = BLE_SM_PAIR_KEY_DIST_ID | BLE_SM_PAIR_KEY_DIST_ENC;
    ble_hs_cfg.sm_their_key_dist |= BLE_SM_PAIR_KEY_DIST_ID | BLE_SM_PAIR_KEY_DIST_ENC;

    return ESP_OK;

}

// Connection state for reconnection logic
typedef enum {
    CONN_STATE_IDLE = 0,
    CONN_STATE_ADVERTISING,
    CONN_STATE_CONNECTED,
    CONN_STATE_DISCONNECTED,
} conn_state_t;

static conn_state_t s_conn_state = CONN_STATE_IDLE;
static uint16_t s_conn_handle = 0;

// Bonded peer address for directed advertising
static ble_addr_t s_last_bonded_peer = {0};
static bool s_has_bonded_peer = false;

// Keepalive task handle
static TaskHandle_t s_keepalive_task = NULL;
#define KEEPALIVE_INTERVAL_MS 30000
#define RSSI_WARNING_THRESHOLD  -70
#define RSSI_CRITICAL_THRESHOLD -85

// Forward declarations
static void start_advertising_with_retry(void);
static esp_err_t start_directed_advertising(const ble_addr_t *peer_addr);
static void keepalive_task(void *pvParameters);

// Get disconnect reason string for debugging
static const char* get_disconnect_reason_str(uint8_t reason)
{
    switch (reason) {
    case 0x08: return "CONNECTION_TIMEOUT";
    case 0x13: return "REMOTE_USER_TERMINATED";
    case 0x16: return "LOCAL_HOST_TERMINATED";
    case 0x05: return "AUTHENTICATION_FAILURE";
    case 0x06: return "PIN_OR_KEY_MISSING";
    case 0x3B: return "UNACCEPTABLE_CONN_PARAMS";
    case 0x3D: return "CONN_FAILED_ESTABLISHMENT";
    default:   return "UNKNOWN";
    }
}

// Check if peer is bonded (has stored keys)
static bool is_peer_bonded(const ble_addr_t *peer_addr)
{
    int rc;
    struct ble_store_value_sec value_sec;
    struct ble_store_key_sec key_sec;

    memset(&key_sec, 0, sizeof(key_sec));
    key_sec.peer_addr = *peer_addr;

    rc = ble_store_read_peer_sec(&key_sec, &value_sec);
    return (rc == 0);
}

static int
nimble_hid_gap_event(struct ble_gap_event *event, void *arg)
{
    struct ble_gap_conn_desc desc;
    int rc;

    switch (event->type) {
    case BLE_GAP_EVENT_CONNECT:
        /* A new connection was established or a connection attempt failed. */
        ESP_LOGI(TAG, "connection %s; status=%d",
                event->connect.status == 0 ? "established" : "failed",
                event->connect.status);
        if (event->connect.status == 0) {
            s_conn_state = CONN_STATE_CONNECTED;
            s_conn_handle = event->connect.conn_handle;

            // Get connection details and save peer address for directed advertising
            rc = ble_gap_conn_find(event->connect.conn_handle, &desc);
            if (rc == 0) {
                memcpy(&s_last_bonded_peer, &desc.peer_id_addr, sizeof(ble_addr_t));
                s_has_bonded_peer = true;
                ESP_LOGI(TAG, "Connected to %02X:%02X:%02X:%02X:%02X:%02X, handle=%d",
                         desc.peer_id_addr.val[5], desc.peer_id_addr.val[4],
                         desc.peer_id_addr.val[3], desc.peer_id_addr.val[2],
                         desc.peer_id_addr.val[1], desc.peer_id_addr.val[0],
                         s_conn_handle);
            } else {
                ESP_LOGI(TAG, "Connected, handle=%d", s_conn_handle);
            }

            // Optimize connection parameters for HID responsiveness
            // Priority: stability over power consumption
            struct ble_gap_upd_params conn_params = {
                .itvl_min = 8,              // 10ms (8 * 1.25ms) - fast response
                .itvl_max = 16,             // 20ms (16 * 1.25ms) - max latency 20ms
                .latency = 0,               // No skipping - always respond immediately
                .supervision_timeout = 400, // 4 seconds (400 * 10ms)
            };
            rc = ble_gap_update_params(s_conn_handle, &conn_params);
            if (rc != 0) {
                ESP_LOGW(TAG, "Failed to update connection params: %d", rc);
            } else {
                ESP_LOGI(TAG, "Connection params update requested: itvl=8-16, latency=0, timeout=400");
            }

            // Start keepalive task
            if (s_keepalive_task == NULL) {
                xTaskCreate(keepalive_task, "keepalive", 2048, NULL, 5, &s_keepalive_task);
                ESP_LOGI(TAG, "Keepalive task started");
            }
        } else {
            // Connection failed, restart advertising
            s_conn_state = CONN_STATE_DISCONNECTED;
            ESP_LOGW(TAG, "Connection failed, restarting advertising");
            start_advertising_with_retry();
        }
        return 0;
        break;
    case BLE_GAP_EVENT_DISCONNECT:
        ESP_LOGI(TAG, "Disconnected: reason=0x%02x (%s)",
                 event->disconnect.reason,
                 get_disconnect_reason_str(event->disconnect.reason));
        s_conn_state = CONN_STATE_DISCONNECTED;
        s_conn_handle = 0;

        // Stop keepalive task
        if (s_keepalive_task != NULL) {
            vTaskDelete(s_keepalive_task);
            s_keepalive_task = NULL;
            ESP_LOGI(TAG, "Keepalive task stopped");
        }

        // Handle based on disconnect reason
        switch (event->disconnect.reason) {
        case 0x08:  // CONNECTION_TIMEOUT - try fast reconnect
            ESP_LOGI(TAG, "Connection timeout, attempting directed advertising");
            if (s_has_bonded_peer && is_peer_bonded(&s_last_bonded_peer)) {
                start_directed_advertising(&s_last_bonded_peer);
            } else {
                start_advertising_with_retry();
            }
            break;

        case 0x13:  // REMOTE_USER_TERMINATED - delay before reconnect
            ESP_LOGI(TAG, "Remote user disconnected, waiting before reconnect");
            vTaskDelay(pdMS_TO_TICKS(1000));
            start_advertising_with_retry();
            break;

        case 0x05:  // AUTHENTICATION_FAILURE
        case 0x06:  // PIN_OR_KEY_MISSING
            ESP_LOGW(TAG, "Authentication failed, clearing bond and restarting");
            if (s_has_bonded_peer) {
                ble_store_util_delete_peer(&s_last_bonded_peer);
                s_has_bonded_peer = false;
            }
            start_advertising_with_retry();
            break;

        default:
            ESP_LOGI(TAG, "Auto-restarting advertising after disconnect");
            start_advertising_with_retry();
            break;
        }

        return 0;
    case BLE_GAP_EVENT_CONN_UPDATE:
        /* The central has updated the connection parameters. */
        ESP_LOGI(TAG, "connection updated; status=%d",
                event->conn_update.status);
        return 0;

    case BLE_GAP_EVENT_ADV_COMPLETE:
        ESP_LOGI(TAG, "advertise complete; reason=%d", event->adv_complete.reason);
        // If not connected, restart advertising
        if (s_conn_state != CONN_STATE_CONNECTED) {
            ESP_LOGI(TAG, "Advertising timeout, restarting...");
            start_advertising_with_retry();
        }
        return 0;

    case BLE_GAP_EVENT_SUBSCRIBE:
        ESP_LOGI(TAG, "subscribe event; conn_handle=%d attr_handle=%d "
                "reason=%d prevn=%d curn=%d previ=%d curi=%d\n",
                event->subscribe.conn_handle,
                event->subscribe.attr_handle,
                event->subscribe.reason,
                event->subscribe.prev_notify,
                event->subscribe.cur_notify,
                event->subscribe.prev_indicate,
                event->subscribe.cur_indicate);
        return 0;

    case BLE_GAP_EVENT_MTU:
        ESP_LOGI(TAG, "mtu update event; conn_handle=%d cid=%d mtu=%d",
                event->mtu.conn_handle,
                event->mtu.channel_id,
                event->mtu.value);
        return 0;

    case BLE_GAP_EVENT_ENC_CHANGE:
        /* Encryption has been enabled or disabled for this connection. */
        MODLOG_DFLT(INFO, "encryption change event; status=%d ",
                event->enc_change.status);
        rc = ble_gap_conn_find(event->enc_change.conn_handle, &desc);
        assert(rc == 0);
        ble_hid_task_start_up();
        return 0;

    case BLE_GAP_EVENT_NOTIFY_TX:
        MODLOG_DFLT(INFO, "notify_tx event; conn_handle=%d attr_handle=%d "
                "status=%d is_indication=%d",
                event->notify_tx.conn_handle,
                event->notify_tx.attr_handle,
                event->notify_tx.status,
                event->notify_tx.indication);
        return 0;

    case BLE_GAP_EVENT_REPEAT_PAIRING:
        /* We already have a bond with the peer, but it is attempting to
         * establish a new secure link.  This app sacrifices security for
         * convenience: just throw away the old bond and accept the new link.
         */

        /* Delete the old bond. */
        rc = ble_gap_conn_find(event->repeat_pairing.conn_handle, &desc);
        assert(rc == 0);
        ble_store_util_delete_peer(&desc.peer_id_addr);

        /* Return BLE_GAP_REPEAT_PAIRING_RETRY to indicate that the host should
         * continue with the pairing operation.
         */
        return BLE_GAP_REPEAT_PAIRING_RETRY;

    case BLE_GAP_EVENT_PASSKEY_ACTION:
        ESP_LOGI(TAG, "PASSKEY_ACTION_EVENT started");
        struct ble_sm_io pkey = {0};
        int key = 0;

        if (event->passkey.params.action == BLE_SM_IOACT_DISP) {
            pkey.action = event->passkey.params.action;
            pkey.passkey = 123456; // This is the passkey to be entered on peer
            ESP_LOGI(TAG, "Enter passkey %" PRIu32 "on the peer side", pkey.passkey);
            rc = ble_sm_inject_io(event->passkey.conn_handle, &pkey);
            ESP_LOGI(TAG, "ble_sm_inject_io result: %d", rc);
        } else if (event->passkey.params.action == BLE_SM_IOACT_NUMCMP) {
            ESP_LOGI(TAG, "Accepting passkey..");
            pkey.action = event->passkey.params.action;
            pkey.numcmp_accept = key;
            rc = ble_sm_inject_io(event->passkey.conn_handle, &pkey);
            ESP_LOGI(TAG, "ble_sm_inject_io result: %d", rc);
        } else if (event->passkey.params.action == BLE_SM_IOACT_OOB) {
            static uint8_t tem_oob[16] = {0};
            pkey.action = event->passkey.params.action;
            for (int i = 0; i < 16; i++) {
                pkey.oob[i] = tem_oob[i];
            }
            rc = ble_sm_inject_io(event->passkey.conn_handle, &pkey);
            ESP_LOGI(TAG, "ble_sm_inject_io result: %d", rc);
        } else if (event->passkey.params.action == BLE_SM_IOACT_INPUT) {
            ESP_LOGI(TAG, "Input not supported passing -> 123456");
            pkey.action = event->passkey.params.action;
            pkey.passkey = 123456;
            rc = ble_sm_inject_io(event->passkey.conn_handle, &pkey);
            ESP_LOGI(TAG, "ble_sm_inject_io result: %d", rc);
        }
        return 0;
    }
    return 0;
}
// Start directed advertising to a specific peer for fast reconnection
static esp_err_t start_directed_advertising(const ble_addr_t *peer_addr)
{
    int rc;
    struct ble_gap_adv_params adv_params;

    // Stop any current advertising first
    ble_gap_adv_stop();

    memset(&adv_params, 0, sizeof(adv_params));
    adv_params.conn_mode = BLE_GAP_CONN_MODE_DIR;  // Directed advertising
    adv_params.disc_mode = BLE_GAP_DISC_MODE_NON;  // Not discoverable to others
    adv_params.high_duty_cycle = 1;                // High duty cycle for fast reconnect

    ESP_LOGI(TAG, "Starting directed advertising to %02X:%02X:%02X:%02X:%02X:%02X",
             peer_addr->val[5], peer_addr->val[4], peer_addr->val[3],
             peer_addr->val[2], peer_addr->val[1], peer_addr->val[0]);

    // Directed advertising with 1.28s timeout (BLE spec limit for high duty cycle)
    rc = ble_gap_adv_start(BLE_OWN_ADDR_PUBLIC, peer_addr, 1280,
                           &adv_params, nimble_hid_gap_event, NULL);
    if (rc != 0) {
        ESP_LOGW(TAG, "Directed advertising failed: %d, falling back to undirected", rc);
        // Fall back to normal advertising
        return esp_hid_ble_gap_adv_start();
    }

    s_conn_state = CONN_STATE_ADVERTISING;
    return ESP_OK;
}

// Keepalive task - sends empty HID reports to maintain connection
static void keepalive_task(void *pvParameters)
{
    ESP_LOGI(TAG, "Keepalive task running, interval=%dms", KEEPALIVE_INTERVAL_MS);

    while (1) {
        vTaskDelay(pdMS_TO_TICKS(KEEPALIVE_INTERVAL_MS));

        if (s_conn_state != CONN_STATE_CONNECTED || s_conn_handle == 0) {
            continue;
        }

        // Read RSSI for connection quality monitoring
        int8_t rssi = 0;
        int rc = ble_gap_conn_rssi(s_conn_handle, &rssi);
        if (rc == 0) {
            if (rssi < RSSI_CRITICAL_THRESHOLD) {
                ESP_LOGW(TAG, "Keepalive: RSSI=%d (CRITICAL - connection at risk)", rssi);
            } else if (rssi < RSSI_WARNING_THRESHOLD) {
                ESP_LOGI(TAG, "Keepalive: RSSI=%d (weak signal)", rssi);
            } else {
                ESP_LOGI(TAG, "Keepalive: RSSI=%d (good)", rssi);
            }
        }

        // Send empty HID report as keepalive
        // This is handled by the HID device layer - just log that we're alive
        ESP_LOGD(TAG, "Keepalive: connection active");
    }
}

// Helper to restart advertising with error handling
static void start_advertising_with_retry(void)
{
    // Small delay before restarting to avoid rapid cycling
    vTaskDelay(pdMS_TO_TICKS(100));

    int rc = esp_hid_ble_gap_adv_start();
    if (rc != 0) {
        ESP_LOGW(TAG, "Failed to restart advertising: %d, will retry", rc);
        // Schedule another retry after longer delay
        vTaskDelay(pdMS_TO_TICKS(1000));
        rc = esp_hid_ble_gap_adv_start();
        if (rc != 0) {
            ESP_LOGE(TAG, "Advertising restart failed again: %d", rc);
        }
    } else {
        s_conn_state = CONN_STATE_ADVERTISING;
        ESP_LOGI(TAG, "Advertising restarted successfully");
    }
}

esp_err_t esp_hid_ble_gap_adv_start(void)
{
    int rc;
    struct ble_gap_adv_params adv_params;
    /* Indefinite advertising for HID device (0 = no timeout) */
    int32_t adv_duration_ms = BLE_HS_FOREVER;

    rc = ble_gap_adv_set_fields(&fields);
    if (rc != 0) {
        MODLOG_DFLT(ERROR, "error setting advertisement data; rc=%d\n", rc);
        return rc;
    }
    /* Begin advertising. */
    memset(&adv_params, 0, sizeof adv_params);
    adv_params.conn_mode = BLE_GAP_CONN_MODE_UND;
    adv_params.disc_mode = BLE_GAP_DISC_MODE_GEN;
    adv_params.itvl_min = BLE_GAP_ADV_ITVL_MS(30);/* Recommended interval 30ms to 50ms */
    adv_params.itvl_max = BLE_GAP_ADV_ITVL_MS(50);
    rc = ble_gap_adv_start(BLE_OWN_ADDR_PUBLIC, NULL, adv_duration_ms,
                           &adv_params, nimble_hid_gap_event, NULL);
    if (rc != 0) {
        MODLOG_DFLT(ERROR, "error enabling advertisement; rc=%d\n", rc);
        return rc;
    }
    return rc;
}
#endif


/*
 * CONTROLLER INIT
 * */

#if !CONFIG_BT_NIMBLE_ENABLED
static esp_err_t init_low_level(uint8_t mode)
{
    esp_err_t ret;
    esp_bt_controller_config_t bt_cfg = BT_CONTROLLER_INIT_CONFIG_DEFAULT();
#if CONFIG_IDF_TARGET_ESP32
    bt_cfg.mode = mode;
#endif
#if CONFIG_BT_HID_DEVICE_ENABLED
    if (mode & ESP_BT_MODE_CLASSIC_BT) {
        bt_cfg.bt_max_acl_conn = 3;
        bt_cfg.bt_max_sync_conn = 3;
    } else
#endif
    {
        ret = esp_bt_controller_mem_release(ESP_BT_MODE_CLASSIC_BT);
        if (ret) {
            ESP_LOGE(TAG, "esp_bt_controller_mem_release failed: %d", ret);
            return ret;
        }
    }
    ret = esp_bt_controller_init(&bt_cfg);
    if (ret) {
        ESP_LOGE(TAG, "esp_bt_controller_init failed: %d", ret);
        return ret;
    }

    ret = esp_bt_controller_enable(mode);
    if (ret) {
        ESP_LOGE(TAG, "esp_bt_controller_enable failed: %d", ret);
        return ret;
    }

    esp_bluedroid_config_t bluedroid_cfg = BT_BLUEDROID_INIT_CONFIG_DEFAULT();
#if (CONFIG_EXAMPLE_SSP_ENABLED == false)
    bluedroid_cfg.ssp_en = false;
#endif
    ret = esp_bluedroid_init_with_cfg(&bluedroid_cfg);
    if (ret) {
        ESP_LOGE(TAG, "esp_bluedroid_init failed: %d", ret);
        return ret;
    }

    ret = esp_bluedroid_enable();
    if (ret) {
        ESP_LOGE(TAG, "esp_bluedroid_enable failed: %d", ret);
        return ret;
    }
#if CONFIG_BT_HID_DEVICE_ENABLED
    if (mode & ESP_BT_MODE_CLASSIC_BT) {
        ret = init_bt_gap();
        if (ret) {
            return ret;
        }
    }
#endif
#if CONFIG_BT_BLE_ENABLED
    if (mode & ESP_BT_MODE_BLE) {
        ret = init_ble_gap();
        if (ret) {
            return ret;
        }
    }
#endif /* CONFIG_BT_BLE_ENABLED */
    return ret;
}
#endif

#if CONFIG_BT_NIMBLE_ENABLED
static esp_err_t init_low_level(uint8_t mode)
{
    esp_err_t ret;
    esp_bt_controller_config_t bt_cfg = BT_CONTROLLER_INIT_CONFIG_DEFAULT();
#if CONFIG_IDF_TARGET_ESP32
    bt_cfg.mode = mode;
#endif
    ret = esp_bt_controller_mem_release(ESP_BT_MODE_CLASSIC_BT);
    if (ret) {
        ESP_LOGE(TAG, "esp_bt_controller_mem_release failed: %d", ret);
        return ret;
    }
    ret = esp_bt_controller_init(&bt_cfg);
    if (ret) {
        ESP_LOGE(TAG, "esp_bt_controller_init failed: %d", ret);
        return ret;
    }

    ret = esp_bt_controller_enable(mode);
    if (ret) {
        ESP_LOGE(TAG, "esp_bt_controller_enable failed: %d", ret);
        return ret;
    }

    ret = esp_nimble_init();
    if (ret) {
        ESP_LOGE(TAG, "esp_nimble_init failed: %d", ret);
        return ret;
    }


    return ret;
}
#endif

esp_err_t esp_hid_gap_init(uint8_t mode)
{
    esp_err_t ret;
    if (!mode || mode > ESP_BT_MODE_BTDM) {
        ESP_LOGE(TAG, "Invalid mode given!");
        return ESP_FAIL;
    }

    if (bt_hidh_cb_semaphore != NULL) {
        ESP_LOGE(TAG, "Already initialised");
        return ESP_FAIL;
    }

    bt_hidh_cb_semaphore = xSemaphoreCreateBinary();
    if (bt_hidh_cb_semaphore == NULL) {
        ESP_LOGE(TAG, "xSemaphoreCreateMutex failed!");
        return ESP_FAIL;
    }

    ble_hidh_cb_semaphore = xSemaphoreCreateBinary();
    if (ble_hidh_cb_semaphore == NULL) {
        ESP_LOGE(TAG, "xSemaphoreCreateMutex failed!");
        vSemaphoreDelete(bt_hidh_cb_semaphore);
        bt_hidh_cb_semaphore = NULL;
        return ESP_FAIL;
    }

    ret = init_low_level(mode);
    if (ret != ESP_OK) {
        vSemaphoreDelete(bt_hidh_cb_semaphore);
        bt_hidh_cb_semaphore = NULL;
        vSemaphoreDelete(ble_hidh_cb_semaphore);
        ble_hidh_cb_semaphore = NULL;
        return ret;
    }

    return ESP_OK;
}

#if CONFIG_BT_NIMBLE_ENABLED
// Public API implementations

void keepalive_start(void)
{
    if (s_keepalive_task == NULL && s_conn_state == CONN_STATE_CONNECTED) {
        xTaskCreate(keepalive_task, "keepalive", 2048, NULL, 5, &s_keepalive_task);
        ESP_LOGI(TAG, "Keepalive task started manually");
    }
}

void keepalive_stop(void)
{
    if (s_keepalive_task != NULL) {
        vTaskDelete(s_keepalive_task);
        s_keepalive_task = NULL;
        ESP_LOGI(TAG, "Keepalive task stopped manually");
    }
}

bool esp_hid_ble_is_connected(void)
{
    return (s_conn_state == CONN_STATE_CONNECTED);
}

uint16_t esp_hid_ble_get_conn_handle(void)
{
    return s_conn_handle;
}
#endif

#if !CONFIG_BT_NIMBLE_ENABLED
esp_err_t esp_hid_scan(uint32_t seconds, size_t *num_results, esp_hid_scan_result_t **results)
{
    if (num_bt_scan_results || bt_scan_results || num_ble_scan_results || ble_scan_results) {
        ESP_LOGE(TAG, "There are old scan results. Free them first!");
        return ESP_FAIL;
    }

#if CONFIG_BT_BLE_ENABLED
    if (start_ble_scan(seconds) == ESP_OK) {
        WAIT_BLE_CB();
    } else {
        return ESP_FAIL;
    }
#endif /* CONFIG_BT_BLE_ENABLED */

#if CONFIG_BT_HID_DEVICE_ENABLED
    if (start_bt_scan(seconds) == ESP_OK) {
        WAIT_BT_CB();
    } else {
        return ESP_FAIL;
    }
#endif

    *num_results = num_bt_scan_results + num_ble_scan_results;
    *results = bt_scan_results;
    if (num_bt_scan_results) {
        while (bt_scan_results->next != NULL) {
            bt_scan_results = bt_scan_results->next;
        }
        bt_scan_results->next = ble_scan_results;
    } else {
        *results = ble_scan_results;
    }

    num_bt_scan_results = 0;
    bt_scan_results = NULL;
    num_ble_scan_results = 0;
    ble_scan_results = NULL;
    return ESP_OK;
}
#endif
