RogerHao/cosmo-pager-radio-demo/firmware/main/esp_hid_gap.h

/*
 * SPDX-FileCopyrightText: 2021-2023 Espressif Systems (Shanghai) CO LTD
 *
 * SPDX-License-Identifier: Unlicense OR CC0-1.0
 */

#ifndef _ESP_HID_GAP_H_
#define _ESP_HID_GAP_H_

#define HIDD_IDLE_MODE 0x00
#define HIDD_BLE_MODE 0x01
#define HIDD_BT_MODE 0x02
#define HIDD_BTDM_MODE 0x03

#if CONFIG_BT_HID_DEVICE_ENABLED
#if CONFIG_BT_BLE_ENABLED
#define HID_DEV_MODE HIDD_BTDM_MODE
#else
#define HID_DEV_MODE HIDD_BT_MODE
#endif
#elif CONFIG_BT_BLE_ENABLED
#define HID_DEV_MODE HIDD_BLE_MODE
#elif CONFIG_BT_NIMBLE_ENABLED
#define HID_DEV_MODE HIDD_BLE_MODE
#else
#define HID_DEV_MODE HIDD_IDLE_MODE
#endif

#include "esp_err.h"
#include "esp_log.h"

#include "esp_bt.h"
#if !CONFIG_BT_NIMBLE_ENABLED
#include "esp_bt_defs.h"
#include "esp_bt_main.h"
#include "esp_gap_bt_api.h"
#endif
#include "esp_hid_common.h"
#if CONFIG_BT_BLE_ENABLED
#include "esp_gattc_api.h"
#include "esp_gatt_defs.h"
#include "esp_gap_ble_api.h"
#endif

#ifdef __cplusplus
extern "C" {
#endif

#if !CONFIG_BT_NIMBLE_ENABLED
typedef struct esp_hidh_scan_result_s {
    struct esp_hidh_scan_result_s *next;

    esp_bd_addr_t bda;
    const char *name;
    int8_t rssi;
    esp_hid_usage_t usage;
    esp_hid_transport_t transport; //BT, BLE or USB
    union {
        struct {
            esp_bt_cod_t cod;
            esp_bt_uuid_t uuid;
        } bt;
        struct {
            esp_ble_addr_type_t addr_type;
            uint16_t appearance;
        } ble;
    };
} esp_hid_scan_result_t;

esp_err_t esp_hid_scan(uint32_t seconds, size_t *num_results, esp_hid_scan_result_t **results);
void esp_hid_scan_results_free(esp_hid_scan_result_t *results);
const char *ble_addr_type_str(esp_ble_addr_type_t ble_addr_type);
void print_uuid(esp_bt_uuid_t *uuid);
#endif

esp_err_t esp_hid_gap_init(uint8_t mode);

esp_err_t esp_hid_ble_gap_adv_init(uint16_t appearance, const char *device_name);
esp_err_t esp_hid_ble_gap_adv_start(void);

#if CONFIG_BT_NIMBLE_ENABLED
/**
 * @brief Start/stop keepalive task for connection monitoring
 */
void keepalive_start(void);
void keepalive_stop(void);

/**
 * @brief Check if currently connected
 * @return true if BLE HID is connected
 */
bool esp_hid_ble_is_connected(void);

/**
 * @brief Get current connection handle
 * @return Connection handle or 0 if not connected
 */
uint16_t esp_hid_ble_get_conn_handle(void);
#endif

#ifdef __cplusplus
}
#endif

#endif /* _ESP_HIDH_GAP_H_ */
